Colatino/zeropedal/pictures/assembly/WhatsApp Image 2022-07-04 at 21.12.30 (3).jpeg

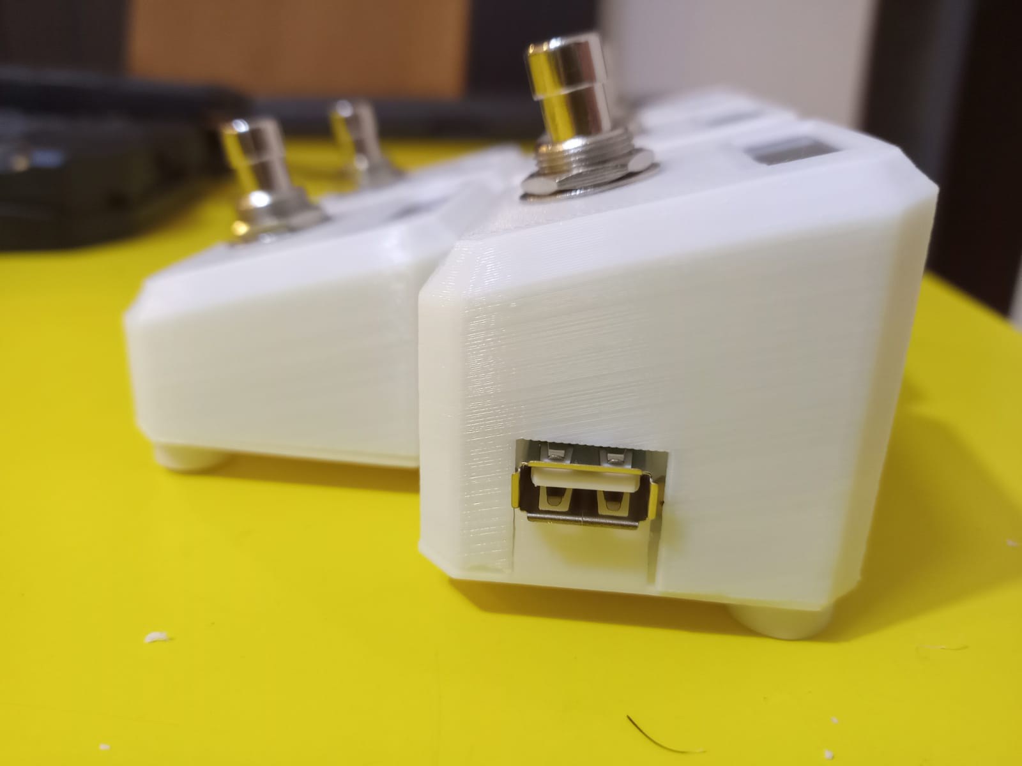
pictures/assembly/WhatsApp Image 2022-07-04 at 21.12.30 (3).jpeg
