Colatino/zeropedal/g1xfour.py

# Effects list for the Zoom G1XFour
# Each effect on this list follows the format:
# ['name',id,group,'filename',nslots,nparam,[params]]
# 'name' - display name of the effect on the pedal
# id - unique identification number for that effect as given by zoom
# group - the group number
# 'filename' - name of the pedal icon file
# nslots - number of slots that the effect occupies on the chain
# nparam - number of parameters for the effect
# param - list of the parameters for this effect with the format:
# [pedal,min,max,cur,'name']
# pedal - bool that tells if the effect makes use of the expression pedal 
# min - minimum value for the parameter
# max - maximum value for the parameter
# cur - current value for the parameter
# 'name' - display name of the parameter
effects = [
['Bypass',0,0,'',1,0,[[0, 0, 0, 0, '-'],[0, 0, 0, 0, '-'],[0, 0, 0, 0, '-'],[0, 0, 0, 0, '-'],[0, 0, 0, 0, '-'],[0, 0, 0, 0, '-'],[0, 0, 0, 0, '-'],[0, 0, 0, 0, '-']]],
['Comp',16777232,1,'COMP.ZD2.BMP',1,4,[[0, 10, 6, 0, 'Sense'],[0, 1, 0, 0, 'ATTCK'],[0, 10, 6, 0, 'Tone'],[0, 100, 80, 0, 'VOL'],[0, 0, 0, 0, '-'],[0, 0, 0, 0, '-'],[0, 0, 0, 0, '-'],[0, 0, 0, 0, '-']]],
['RackComp',16777248,1,'RACKCOMP.ZD2.BMP',1,4,[[0, 50, 40, 0, 'THRSH'],[0, 9, 5, 0, 'Ratio'],[0, 9, 6, 0, 'ATTCK'],[0, 100, 80, 0, 'VOL'],[0, 0, 0, 0, '-'],[0, 0, 0, 0, '-'],[0, 0, 0, 0, '-'],[0, 0, 0, 0, '-']]],
['SlowATTCK',16777264,1,'SLWATK.ZD2.BMP',1,4,[[0, 49, 20, 0, 'Time'],[0, 10, 10, 0, 'Curve'],[0, 100, 100, 0, 'Tone'],[0, 100, 80, 0, 'VOL'],[0, 0, 0, 0, '-'],[0, 0, 0, 0, '-'],[0, 0, 0, 0, '-'],[0, 0, 0, 0, '-']]],
['ZNR',16777280,1,'ZNR.ZD2.BMP',1,4,[[0, 1, 1, 0, 'DETCT'],[0, 100, 100, 0, 'Depth'],[0, 100, 30, 0, 'THRSH'],[0, 100, 0, 0, 'Decay'],[0, 0, 0, 0, '-'],[0, 0, 0, 0, '-'],[0, 0, 0, 0, '-'],[0, 0, 0, 0, '-']]],
['MuteSW',16777296,1,'MUTESW.ZD2.BMP',1,4,[[0, 100, 13, 0, 'Edge'],[0, 100, 100, 0, 'Speed'],[0, 1, 0, 0, 'INVRT'],[0, 2, 1, 0, 'ON/OFF'],[0, 0, 0, 0, '-'],[0, 0, 0, 0, '-'],[0, 0, 0, 0, '-'],[0, 0, 0, 0, '-']]],
['GrayComp',16777312,1,'GRAYCOMP.ZD2.BMP',1,4,[[0, 100, 63, 0, 'SUSTN'],[0, 100, 50, 0, 'Lo'],[0, 100, 50, 0, 'Hi'],[0, 100, 88, 0, 'VOL'],[0, 0, 0, 0, '-'],[0, 0, 0, 0, '-'],[0, 0, 0, 0, '-'],[0, 0, 0, 0, '-']]],
['NoiseGate',16777328,1,'N_GATE.ZD2.BMP',1,4,[[0, 1, 1, 0, 'DETCT'],[0, 100, 100, 0, 'Depth'],[0, 100, 54, 0, 'THRSH'],[0, 100, 0, 0, 'Decay'],[0, 0, 0, 0, '-'],[0, 0, 0, 0, '-'],[0, 0, 0, 0, '-'],[0, 0, 0, 0, '-']]],
['OptComp',16777344,1,'OPTCOMP.ZD2.BMP',1,4,[[0, 10, 7, 0, 'Drive'],[0, 100, 50, 0, 'Lo'],[0, 100, 50, 0, 'Hi'],[0, 100, 60, 0, 'VOL'],[0, 0, 0, 0, '-'],[0, 0, 0, 0, '-'],[0, 0, 0, 0, '-'],[0, 0, 0, 0, '-']]],
['BlackOpt',25165840,1,'BLACKOPT.ZD2.BMP',1,4,[[0, 100, 50, 0, 'Comp'],[0, 100, 50, 0, 'Lo'],[0, 100, 50, 0, 'Hi'],[0, 100, 76, 0, 'VOL'],[0, 0, 0, 0, '-'],[0, 0, 0, 0, '-'],[0, 0, 0, 0, '-'],[0, 0, 0, 0, '-']]],
['LMT-76',25165856,1,'LMT1176.ZD2.BMP',1,4,[[0, 80, 40, 0, 'Input'],[0, 3, 0, 0, 'Ratio'],[0, 60, 10, 0, 'REL'],[0, 80, 38, 0, 'Output'],[0, 0, 0, 0, '-'],[0, 0, 0, 0, '-'],[0, 0, 0, 0, '-'],[0, 0, 0, 0, '-']]],
['AutoWah',33554448,2,'AUTOWAH.ZD2.BMP',1,4,[[0, 1, 1, 0, 'Mode'],[0, 9, 7, 0, 'Sense'],[0, 10, 8, 0, 'RESO'],[0, 100, 80, 0, 'VOL'],[0, 0, 0, 0, '-'],[0, 0, 0, 0, '-'],[0, 0, 0, 0, '-'],[0, 0, 0, 0, '-']]],
['Resonance',33554464,2,'RESONANC.ZD2.BMP',1,4,[[0, 1, 1, 0, 'Mode'],[0, 9, 4, 0, 'Sense'],[0, 10, 8, 0, 'RESO'],[0, 100, 80, 0, 'VOL'],[0, 0, 0, 0, '-'],[0, 0, 0, 0, '-'],[0, 0, 0, 0, '-'],[0, 0, 0, 0, '-']]],
['Cry',33554480,2,'CRY.ZD2.BMP',1,4,[[0, 9, 6, 0, 'Range'],[0, 10, 8, 0, 'RESO'],[0, 19, 16, 0, 'Sense'],[0, 100, 100, 0, 'BAL'],[0, 0, 0, 0, '-'],[0, 0, 0, 0, '-'],[0, 0, 0, 0, '-'],[0, 0, 0, 0, '-']]],
['SeqFLTR',33554496,2,'SEQFLTR.ZD2.BMP',1,4,[[0, 6, 6, 0, 'Step'],[0, 7, 6, 0, 'PTTRN'],[0, 77, 25, 0, 'Speed'],[0, 10, 10, 0, 'RESO'],[0, 0, 0, 0, '-'],[0, 0, 0, 0, '-'],[0, 0, 0, 0, '-'],[0, 0, 0, 0, '-']]],
['Gt GEQ',33554513,2,'GT_GEQ1U.ZD2.BMP',2,7,[[0, 48, 24, 0, '160'],[0, 48, 24, 0, '400'],[0, 48, 24, 0, '800'],[0, 48, 24, 0, '3.2k'],[0, 48, 24, 0, '6.4k'],[0, 48, 24, 0, '12k'],[0, 100, 80, 0, 'VOL'],[0, 0, 0, 0, '-']]],
['Gt GEQ 7',33554516,2,'GTGEQ71U.ZD2.BMP',2,8,[[0, 48, 24, 0, '100'],[0, 48, 24, 0, '200'],[0, 48, 24, 0, '400'],[0, 48, 24, 0, '800'],[0, 48, 24, 0, '1.6k'],[0, 48, 24, 0, '3.2k'],[0, 48, 24, 0, '6.4k'],[0, 100, 80, 0, 'VOL']]],
['St Gt GEQ',33554529,2,'STGTGE1U.ZD2.BMP',2,7,[[0, 48, 24, 0, '160'],[0, 48, 24, 0, '400'],[0, 48, 24, 0, '800'],[0, 48, 24, 0, '3.2k'],[0, 48, 24, 0, '6.4k'],[0, 48, 24, 0, '12k'],[0, 100, 80, 0, 'VOL'],[0, 0, 0, 0, '-']]],
['ParaEQ',33554544,2,'PARAEQ.ZD2.BMP',1,4,[[0, 30, 8, 0, 'FREQ'],[0, 67, 1, 0, 'Q'],[0, 48, 24, 0, 'Gain'],[0, 100, 80, 0, 'VOL'],[0, 0, 0, 0, '-'],[0, 0, 0, 0, '-'],[0, 0, 0, 0, '-'],[0, 0, 0, 0, '-']]],
['RndmFLTR',33554576,2,'RNDMFLTR.ZD2.BMP',1,4,[[0, 2, 2, 0, 'Type'],[0, 77, 34, 0, 'Speed'],[0, 100, 90, 0, 'BAL'],[0, 100, 80, 0, 'VOL'],[0, 0, 0, 0, '-'],[0, 0, 0, 0, '-'],[0, 0, 0, 0, '-'],[0, 0, 0, 0, '-']]],
['LowPassFL',33554592,2,'LOWPASSF.ZD2.BMP',1,4,[[0, 100, 56, 0, 'FREQ'],[0, 201, 50, 0, 'Sense'],[0, 21, 3, 0, 'RESO'],[0, 100, 100, 0, 'BAL'],[0, 0, 0, 0, '-'],[0, 0, 0, 0, '-'],[0, 0, 0, 0, '-'],[0, 0, 0, 0, '-']]],
['Exciter',33554608,2,'EXCITER.ZD2.BMP',1,4,[[0, 100, 0, 0, 'Bass'],[0, 100, 0, 0, 'Treble'],[0, 100, 80, 0, 'VOL'],[0, 1, 0, 0, 'ON/OFF'],[0, 0, 0, 0, '-'],[0, 0, 0, 0, '-'],[0, 0, 0, 0, '-'],[0, 0, 0, 0, '-']]],
['Step',33554624,2,'STEP.ZD2.BMP',1,4,[[0, 100, 60, 0, 'Depth'],[0, 78, 25, 0, 'Rate'],[0, 10, 8, 0, 'RESO'],[0, 10, 10, 0, 'Shape'],[0, 0, 0, 0, '-'],[0, 0, 0, 0, '-'],[0, 0, 0, 0, '-'],[0, 0, 0, 0, '-']]],
['LFO FLTR',33554640,2,'LFO_FLTR.ZD2.BMP',1,4,[[0, 100, 100, 0, 'Depth'],[0, 77, 57, 0, 'Rate'],[0, 10, 8, 0, 'RESO'],[0, 3, 0, 0, 'Wave'],[0, 0, 0, 0, '-'],[0, 0, 0, 0, '-'],[0, 0, 0, 0, '-'],[0, 0, 0, 0, '-']]],
['TS Drive',50331664,3,'TS_DRIVE.ZD2.BMP',1,4,[[0, 100, 74, 0, 'Gain'],[0, 1, 0, 0, 'Boost'],[0, 100, 57, 0, 'Tone'],[0, 100, 82, 0, 'VOL'],[0, 0, 0, 0, '-'],[0, 0, 0, 0, '-'],[0, 0, 0, 0, '-'],[0, 0, 0, 0, '-']]],
['EP Stomp',50331680,3,'EP_STOMP.ZD2.BMP',1,4,[[0, 100, 35, 0, 'Gain'],[0, 20, 10, 0, 'Bass'],[0, 20, 8, 0, 'Treble'],[0, 100, 62, 0, 'VOL'],[0, 0, 0, 0, '-'],[0, 0, 0, 0, '-'],[0, 0, 0, 0, '-'],[0, 0, 0, 0, '-']]],
['RC Boost',50331696,3,'RCBOOST.ZD2.BMP',1,4,[[0, 100, 58, 0, 'Gain'],[0, 100, 48, 0, 'Bass'],[0, 100, 52, 0, 'Treble'],[0, 100, 48, 0, 'VOL'],[0, 0, 0, 0, '-'],[0, 0, 0, 0, '-'],[0, 0, 0, 0, '-'],[0, 0, 0, 0, '-']]],
['GoldDrive',50331712,3,'GOLD_DRV.ZD2.BMP',1,4,[[0, 100, 69, 0, 'Gain'],[0, 100, 50, 0, 'Bass'],[0, 100, 56, 0, 'Treble'],[0, 100, 43, 0, 'VOL'],[0, 0, 0, 0, '-'],[0, 0, 0, 0, '-'],[0, 0, 0, 0, '-'],[0, 0, 0, 0, '-']]],
['SweetDrv',50331728,3,'SWEETDRV.ZD2.BMP',1,4,[[0, 100, 78, 0, 'Gain'],[0, 100, 50, 0, 'Tone'],[0, 100, 67, 0, 'Focus'],[0, 100, 62, 0, 'VOL'],[0, 0, 0, 0, '-'],[0, 0, 0, 0, '-'],[0, 0, 0, 0, '-'],[0, 0, 0, 0, '-']]],
['DYN Drive',50331744,3,'DYNDRIVE.ZD2.BMP',1,4,[[0, 100, 78, 0, 'Gain'],[0, 100, 67, 0, 'Tone'],[0, 1, 1, 0, 'Mode'],[0, 100, 46, 0, 'VOL'],[0, 0, 0, 0, '-'],[0, 0, 0, 0, '-'],[0, 0, 0, 0, '-'],[0, 0, 0, 0, '-']]],
['RedCrunch',50331760,3,'REDCRUNC.ZD2.BMP',1,4,[[0, 100, 68, 0, 'Gain'],[0, 100, 47, 0, 'Tone'],[0, 100, 48, 0, 'PRSNC'],[0, 100, 61, 0, 'VOL'],[0, 0, 0, 0, '-'],[0, 0, 0, 0, '-'],[0, 0, 0, 0, '-'],[0, 0, 0, 0, '-']]],
['MetalWRLD',50331776,3,'MTLWRLD.ZD2.BMP',1,4,[[0, 100, 60, 0, 'Gain'],[0, 100, 50, 0, 'Bass'],[0, 100, 50, 0, 'Treble'],[0, 100, 80, 0, 'VOL'],[0, 0, 0, 0, '-'],[0, 0, 0, 0, '-'],[0, 0, 0, 0, '-'],[0, 0, 0, 0, '-']]],
['TB MK1.5',50331792,3,'TB_MK15.ZD2.BMP',1,4,[[0, 100, 90, 0, 'ATTCK'],[0, 100, 100, 0, 'Tone'],[0, 1, 1, 0, 'Color'],[0, 100, 92, 0, 'VOL'],[0, 0, 0, 0, '-'],[0, 0, 0, 0, '-'],[0, 0, 0, 0, '-'],[0, 0, 0, 0, '-']]],
['OctFuzz',50331808,3,'OCTFUZZ.ZD2.BMP',1,4,[[0, 100, 65, 0, 'Boost'],[0, 1, 1, 0, 'Color'],[0, 100, 50, 0, 'Tone'],[0, 100, 68, 0, 'VOL'],[0, 0, 0, 0, '-'],[0, 0, 0, 0, '-'],[0, 0, 0, 0, '-'],[0, 0, 0, 0, '-']]],
['SpotBoost',50331824,3,'SPTBOOST.ZD2.BMP',1,4,[[0, 100, 35, 0, 'Boost'],[0, 20, 10, 0, 'Bass'],[0, 20, 8, 0, 'Treble'],[0, 1, 1, 0, 'ON/OFF'],[0, 0, 0, 0, '-'],[0, 0, 0, 0, '-'],[0, 0, 0, 0, '-'],[0, 0, 0, 0, '-']]],
['Aco.Sim',50331840,3,'ACOSIM.ZD2.BMP',1,4,[[0, 100, 80, 0, 'Top'],[0, 100, 50, 0, 'Body'],[0, 100, 100, 0, 'Tone'],[0, 100, 80, 0, 'VOL'],[0, 0, 0, 0, '-'],[0, 0, 0, 0, '-'],[0, 0, 0, 0, '-'],[0, 0, 0, 0, '-']]],
['NYC Muff',50331856,3,'NYC_MUFF.ZD2.BMP',1,4,[[0, 100, 70, 0, 'SUSTN'],[0, 100, 55, 0, 'Tone'],[0, 100, 100, 0, 'BAL'],[0, 100, 58, 0, 'VOL'],[0, 0, 0, 0, '-'],[0, 0, 0, 0, '-'],[0, 0, 0, 0, '-'],[0, 0, 0, 0, '-']]],
['HG THRTTL',50331872,3,'BGTHRTTL.ZD2.BMP',1,4,[[0, 100, 78, 0, 'Gain'],[0, 100, 56, 0, 'Tone'],[0, 100, 46, 0, 'MdCut'],[0, 100, 54, 0, 'VOL'],[0, 0, 0, 0, '-'],[0, 0, 0, 0, '-'],[0, 0, 0, 0, '-'],[0, 0, 0, 0, '-']]],
['BG GRID',50331888,3,'BG_GRID.ZD2.BMP',1,4,[[0, 100, 68, 0, 'Gain'],[0, 100, 50, 0, 'Tone'],[0, 100, 100, 0, 'BAL'],[0, 100, 74, 0, 'VOL'],[0, 0, 0, 0, '-'],[0, 0, 0, 0, '-'],[0, 0, 0, 0, '-'],[0, 0, 0, 0, '-']]],
['DIST 1',50331936,3,'DIST_1.ZD2.BMP',1,4,[[0, 100, 61, 0, 'Gain'],[0, 100, 41, 0, 'Tone'],[0, 100, 100, 0, 'VOL'],[0, 1, 0, 0, 'Comp'],[0, 0, 0, 0, '-'],[0, 0, 0, 0, '-'],[0, 0, 0, 0, '-'],[0, 0, 0, 0, '-']]],
['Squeak',50331952,3,'SQUEAK.ZD2.BMP',1,4,[[0, 100, 47, 0, 'Gain'],[0, 100, 60, 0, 'FLTR'],[0, 100, 79, 0, 'VOL'],[0, 100, 0, 0, 'DryMx'],[0, 0, 0, 0, '-'],[0, 0, 0, 0, '-'],[0, 0, 0, 0, '-'],[0, 0, 0, 0, '-']]],
['UpOctBSTR',50331968,3,'UPOCTBST.ZD2.BMP',1,4,[[0, 100, 65, 0, 'UpOct'],[0, 100, 47, 0, 'DryMx'],[0, 100, 75, 0, 'Bottom'],[0, 100, 70, 0, 'PRSNC'],[0, 0, 0, 0, '-'],[0, 0, 0, 0, '-'],[0, 0, 0, 0, '-'],[0, 0, 0, 0, '-']]],
['OutputBST',50331984,3,'OUT_BST.ZD2.BMP',1,4,[[0, 9, 4, 0, 'Range'],[0, 100, 30, 0, 'Boost'],[0, 100, 50, 0, 'Tone'],[0, 100, 80, 0, 'VOL'],[0, 0, 0, 0, '-'],[0, 0, 0, 0, '-'],[0, 0, 0, 0, '-'],[0, 0, 0, 0, '-']]],
['DIST Plus',50332000,3,'DISTPLUS.ZD2.BMP',1,4,[[0, 100, 70, 0, 'Gain'],[0, 100, 100, 0, 'VOL'],[0, 100, 0, 0, 'DryMx'],[0, 2, 0, 0, 'Comp'],[0, 0, 0, 0, '-'],[0, 0, 0, 0, '-'],[0, 0, 0, 0, '-'],[0, 0, 0, 0, '-']]],
['Zen O.DRV',50332016,3,'ZEN_DRV.ZD2.BMP',1,4,[[0, 100, 70, 0, 'Gain'],[0, 100, 60, 0, 'Tone'],[0, 100, 80, 0, 'Voice'],[0, 100, 70, 0, 'VOL'],[0, 0, 0, 0, '-'],[0, 0, 0, 0, '-'],[0, 0, 0, 0, '-'],[0, 0, 0, 0, '-']]],
['VioletDST',50332048,3,'VIOLETDS.ZD2.BMP',1,4,[[0, 100, 70, 0, 'Gain'],[0, 100, 80, 0, 'Tone'],[0, 2, 2, 0, 'Voice'],[0, 100, 70, 0, 'VOL'],[0, 0, 0, 0, '-'],[0, 0, 0, 0, '-'],[0, 0, 0, 0, '-'],[0, 0, 0, 0, '-']]],
['MS 800',67108881,4,'MS800_1U.ZD2.BMP',2,7,[[0, 1, 1, 0, 'Input'],[0, 100, 50, 0, 'Bass'],[0, 100, 50, 0, 'MID'],[0, 100, 50, 0, 'Treble'],[0, 100, 30, 0, 'PRSNC'],[0, 100, 70, 0, 'Gain'],[0, 100, 70, 0, 'VOL'],[0, 0, 0, 0, '-']]],
['MS 1959',67108889,4,'MS19591U.ZD2.BMP',2,7,[[0, 100, 50, 0, 'Bass'],[0, 100, 70, 0, 'MID'],[0, 100, 60, 0, 'Treble'],[0, 100, 40, 0, 'PRSNC'],[0, 101, 61, 0, 'Input1'],[0, 101, 0, 0, 'Input2'],[0, 100, 80, 0, 'VOL'],[0, 0, 0, 0, '-']]],
['MS 45os',67108891,4,'MS45OS1U.ZD2.BMP',2,7,[[0, 100, 30, 0, 'Bass'],[0, 100, 70, 0, 'MID'],[0, 100, 65, 0, 'Treble'],[0, 100, 30, 0, 'PRSNC'],[0, 101, 61, 0, 'Input1'],[0, 101, 0, 0, 'Input2'],[0, 100, 80, 0, 'VOL'],[0, 0, 0, 0, '-']]],
['FD TWNR',67108897,4,'FD_TWR1U.ZD2.BMP',2,8,[[0, 90, 38, 0, 'Bass'],[0, 90, 40, 0, 'MID'],[0, 90, 35, 0, 'Treble'],[0, 1, 0, 0, 'BRGHT'],[0, 90, 30, 0, 'Gain'],[0, 90, 70, 0, 'VOL'],[0, 90, 0, 0, 'Depth'],[0, 100, 40, 0, 'Speed']]],
['FD B-MAN',67108904,4,'FDBMAN1U.ZD2.BMP',2,7,[[0, 1, 1, 0, 'Input'],[0, 110, 30, 0, 'Bass'],[0, 110, 90, 0, 'MID'],[0, 110, 40, 0, 'Treble'],[0, 110, 50, 0, 'PRSNC'],[0, 110, 30, 0, 'Gain'],[0, 110, 50, 0, 'VOL'],[0, 0, 0, 0, '-']]],
['FD DLXR',67108908,4,'FDDLXR1U.ZD2.BMP',2,7,[[0, 1, 0, 0, 'Input'],[0, 90, 33, 0, 'Bass'],[0, 90, 55, 0, 'Treble'],[0, 90, 50, 0, 'Gain'],[0, 90, 90, 0, 'VOL'],[0, 90, 0, 0, 'Depth'],[0, 100, 40, 0, 'Speed'],[0, 0, 0, 0, '-']]],
['FD MASTER',67108909,4,'FDMSTR1U.ZD2.BMP',2,6,[[0, 90, 40, 0, 'Gain'],[0, 90, 60, 0, 'Bass'],[0, 90, 60, 0, 'MID'],[0, 90, 60, 0, 'Treble'],[0, 1, 1, 0, 'Fat'],[0, 90, 40, 0, 'VOL'],[0, 0, 0, 0, '-'],[0, 0, 0, 0, '-']]],
['UK 30A',67108913,4,'UK30A_1U.ZD2.BMP',2,7,[[0, 100, 49, 0, 'Bass'],[0, 100, 38, 0, 'Treble'],[0, 100, 78, 0, 'Cut'],[0, 100, 30, 0, 'Gain'],[0, 100, 84, 0, 'VOL'],[0, 100, 0, 0, 'Depth'],[0, 110, 50, 0, 'Speed'],[0, 0, 0, 0, '-']]],
['BG MK1',67108929,4,'BGMK1_1U.ZD2.BMP',2,7,[[0, 100, 49, 0, 'Bass'],[0, 100, 55, 0, 'MID'],[0, 100, 53, 0, 'Treble'],[0, 100, 55, 0, 'PRSNC'],[0, 100, 72, 0, 'Gain1'],[0, 100, 70, 0, 'Gain2'],[0, 100, 58, 0, 'VOL'],[0, 0, 0, 0, '-']]],
['BG MK3',67108931,4,'BGMK3_1U.ZD2.BMP',2,7,[[0, 100, 52, 0, 'Bass'],[0, 100, 85, 0, 'MID'],[0, 100, 40, 0, 'Treble'],[0, 100, 40, 0, 'PRSNC'],[0, 100, 75, 0, 'Gain1'],[0, 100, 75, 0, 'Gain2'],[0, 100, 78, 0, 'VOL'],[0, 0, 0, 0, '-']]],
['XtasyBlue',67108945,4,'XTSBLU1U.ZD2.BMP',2,7,[[0, 100, 50, 0, 'Bass'],[0, 100, 50, 0, 'MID'],[0, 100, 50, 0, 'Treble'],[0, 100, 40, 0, 'PRSNC'],[0, 1, 1, 0, 'STRCT'],[0, 100, 60, 0, 'Gain'],[0, 100, 42, 0, 'VOL'],[0, 0, 0, 0, '-']]],
['HW 100',67108961,4,'HW100_1U.ZD2.BMP',2,7,[[0, 1, 1, 0, 'Input'],[0, 100, 40, 0, 'Bass'],[0, 100, 80, 0, 'MID'],[0, 100, 60, 0, 'Treble'],[0, 100, 60, 0, 'PRSNC'],[0, 100, 50, 0, 'Gain'],[0, 100, 60, 0, 'VOL'],[0, 0, 0, 0, '-']]],
['Recti ORG',67108977,4,'RCTORG1U.ZD2.BMP',2,7,[[0, 1, 0, 0, 'Mode'],[0, 100, 52, 0, 'Bass'],[0, 100, 65, 0, 'MID'],[0, 100, 67, 0, 'Treble'],[0, 100, 62, 0, 'PRSNC'],[0, 100, 70, 0, 'Gain'],[0, 100, 62, 0, 'VOL'],[0, 0, 0, 0, '-']]],
['ORG120',67108993,4,'ORG1201U.ZD2.BMP',2,7,[[0, 1, 1, 0, 'Input'],[0, 5, 3, 0, 'Color'],[0, 100, 50, 0, 'Bass'],[0, 100, 60, 0, 'Treble'],[0, 100, 50, 0, 'PRSNC'],[0, 100, 53, 0, 'Gain'],[0, 100, 100, 0, 'VOL'],[0, 0, 0, 0, '-']]],
['DZ DRV',67109009,4,'DZ_DRV1U.ZD2.BMP',2,8,[[0, 100, 50, 0, 'Bass'],[0, 100, 70, 0, 'MID'],[0, 100, 60, 0, 'Treble'],[0, 100, 40, 0, 'PRSNC'],[0, 100, 60, 0, 'Gain'],[0, 100, 80, 0, 'VOL'],[0, 100, 0, 0, 'Deep'],[0, 100, 0, 0, 'MidCut']]],
['MATCH30',67109025,4,'MACH301U.ZD2.BMP',2,7,[[0, 101, 36, 0, 'Gain1'],[0, 100, 47, 0, 'Bass1'],[0, 100, 49, 0, 'TRBL1'],[0, 101, 0, 0, 'Gain2'],[0, 5, 1, 0, 'Tone2'],[0, 100, 0, 0, 'Cut'],[0, 101, 34, 0, 'VOL'],[0, 0, 0, 0, '-']]],
['MS4x12',83886096,5,'MS4X12.ZD2.BMP',1,4,[[0, 1, 0, 0, 'MIC'],[0, 100, 50, 0, 'D57:D421'],[0, 100, 50, 0, 'Hi'],[0, 100, 50, 0, 'Lo'],[0, 0, 0, 0, '-'],[0, 0, 0, 0, '-'],[0, 0, 0, 0, '-'],[0, 0, 0, 0, '-']]],
['MS4x12GB',83886104,5,'MS4X12GB.ZD2.BMP',1,4,[[0, 1, 0, 0, 'MIC'],[0, 100, 50, 0, 'D57:D421'],[0, 100, 50, 0, 'Hi'],[0, 100, 50, 0, 'Lo'],[0, 0, 0, 0, '-'],[0, 0, 0, 0, '-'],[0, 0, 0, 0, '-'],[0, 0, 0, 0, '-']]],
['MS4x12AL',83886106,5,'MS4X12AL.ZD2.BMP',1,4,[[0, 1, 0, 0, 'MIC'],[0, 100, 50, 0, 'D57:D421'],[0, 100, 50, 0, 'Hi'],[0, 100, 50, 0, 'Lo'],[0, 0, 0, 0, '-'],[0, 0, 0, 0, '-'],[0, 0, 0, 0, '-'],[0, 0, 0, 0, '-']]],
['FD2x12',83886112,5,'FD2X12.ZD2.BMP',1,4,[[0, 1, 0, 0, 'MIC'],[0, 100, 50, 0, 'D57:D421'],[0, 100, 50, 0, 'Hi'],[0, 100, 50, 0, 'Lo'],[0, 0, 0, 0, '-'],[0, 0, 0, 0, '-'],[0, 0, 0, 0, '-'],[0, 0, 0, 0, '-']]],
['FD-B4x10',83886119,5,'FDB4X10.ZD2.BMP',1,4,[[0, 1, 0, 0, 'MIC'],[0, 100, 50, 0, 'D57:D421'],[0, 100, 50, 0, 'Hi'],[0, 100, 50, 0, 'Lo'],[0, 0, 0, 0, '-'],[0, 0, 0, 0, '-'],[0, 0, 0, 0, '-'],[0, 0, 0, 0, '-']]],
['FD-DX1x12',83886122,5,'FDDX1X12.ZD2.BMP',1,4,[[0, 1, 0, 0, 'MIC'],[0, 100, 50, 0, 'D57:D421'],[0, 100, 50, 0, 'Hi'],[0, 100, 50, 0, 'Lo'],[0, 0, 0, 0, '-'],[0, 0, 0, 0, '-'],[0, 0, 0, 0, '-'],[0, 0, 0, 0, '-']]],
['FD MA2x12',83886123,5,'FDMA2X12.ZD2.BMP',1,4,[[0, 1, 0, 0, 'MIC'],[0, 100, 50, 0, 'D57:D421'],[0, 100, 50, 0, 'Hi'],[0, 100, 50, 0, 'Lo'],[0, 0, 0, 0, '-'],[0, 0, 0, 0, '-'],[0, 0, 0, 0, '-'],[0, 0, 0, 0, '-']]],
['UK2x12',83886128,5,'UK2X12.ZD2.BMP',1,4,[[0, 1, 0, 0, 'MIC'],[0, 100, 50, 0, 'D57:D421'],[0, 100, 50, 0, 'Hi'],[0, 100, 50, 0, 'Lo'],[0, 0, 0, 0, '-'],[0, 0, 0, 0, '-'],[0, 0, 0, 0, '-'],[0, 0, 0, 0, '-']]],
['MK1 1x12',83886144,5,'MK1_1X12.ZD2.BMP',1,4,[[0, 1, 0, 0, 'MIC'],[0, 100, 50, 0, 'D57:D421'],[0, 100, 50, 0, 'Hi'],[0, 100, 50, 0, 'Lo'],[0, 0, 0, 0, '-'],[0, 0, 0, 0, '-'],[0, 0, 0, 0, '-'],[0, 0, 0, 0, '-']]],
['MK3 1x12',83886146,5,'MK3_1X12.ZD2.BMP',1,4,[[0, 1, 0, 0, 'MIC'],[0, 100, 50, 0, 'D57:D421'],[0, 100, 50, 0, 'Hi'],[0, 100, 50, 0, 'Lo'],[0, 0, 0, 0, '-'],[0, 0, 0, 0, '-'],[0, 0, 0, 0, '-'],[0, 0, 0, 0, '-']]],
['BGN4x12',83886160,5,'BGN4X12.ZD2.BMP',1,4,[[0, 1, 0, 0, 'MIC'],[0, 100, 50, 0, 'D57:D421'],[0, 100, 50, 0, 'Hi'],[0, 100, 50, 0, 'Lo'],[0, 0, 0, 0, '-'],[0, 0, 0, 0, '-'],[0, 0, 0, 0, '-'],[0, 0, 0, 0, '-']]],
['HW4x12',83886176,5,'HW4X12.ZD2.BMP',1,4,[[0, 1, 0, 0, 'MIC'],[0, 100, 50, 0, 'D57:D421'],[0, 100, 50, 0, 'Hi'],[0, 100, 50, 0, 'Lo'],[0, 0, 0, 0, '-'],[0, 0, 0, 0, '-'],[0, 0, 0, 0, '-'],[0, 0, 0, 0, '-']]],
['RCT4x12',83886192,5,'RCT4X12.ZD2.BMP',1,4,[[0, 1, 0, 0, 'MIC'],[0, 100, 50, 0, 'D57:D421'],[0, 100, 50, 0, 'Hi'],[0, 100, 50, 0, 'Lo'],[0, 0, 0, 0, '-'],[0, 0, 0, 0, '-'],[0, 0, 0, 0, '-'],[0, 0, 0, 0, '-']]],
['ORG4x12',83886208,5,'ORG_4X12.ZD2.BMP',1,4,[[0, 1, 0, 0, 'MIC'],[0, 100, 50, 0, 'D57:D421'],[0, 100, 50, 0, 'Hi'],[0, 100, 50, 0, 'Lo'],[0, 0, 0, 0, '-'],[0, 0, 0, 0, '-'],[0, 0, 0, 0, '-'],[0, 0, 0, 0, '-']]],
['DZ4x12F',83886224,5,'DZ4X12F.ZD2.BMP',1,4,[[0, 1, 0, 0, 'MIC'],[0, 100, 50, 0, 'D57:D421'],[0, 100, 50, 0, 'Hi'],[0, 100, 50, 0, 'Lo'],[0, 0, 0, 0, '-'],[0, 0, 0, 0, '-'],[0, 0, 0, 0, '-'],[0, 0, 0, 0, '-']]],
['MA2x12',83886240,5,'MA2X12.ZD2.BMP',1,4,[[0, 1, 0, 0, 'MIC'],[0, 100, 50, 0, 'D57:D421'],[0, 100, 50, 0, 'Hi'],[0, 100, 50, 0, 'Lo'],[0, 0, 0, 0, '-'],[0, 0, 0, 0, '-'],[0, 0, 0, 0, '-'],[0, 0, 0, 0, '-']]],
['Tremolo',100663312,6,'TREMOLO.ZD2.BMP',1,4,[[0, 2, 0, 0, 'Wave'],[0, 100, 90, 0, 'Depth'],[0, 110, 50, 0, 'Rate'],[0, 100, 62, 0, 'VOL'],[0, 0, 0, 0, '-'],[0, 0, 0, 0, '-'],[0, 0, 0, 0, '-'],[0, 0, 0, 0, '-']]],
['Chorus',100663328,6,'CHORUS.ZD2.BMP',1,4,[[0, 100, 40, 0, 'Depth'],[0, 49, 24, 0, 'Rate'],[0, 10, 7, 0, 'Tone'],[0, 100, 50, 0, 'Mix'],[0, 0, 0, 0, '-'],[0, 0, 0, 0, '-'],[0, 0, 0, 0, '-'],[0, 0, 0, 0, '-']]],
['StereoCho',100663344,6,'STEREOCH.ZD2.BMP',1,4,[[0, 100, 80, 0, 'Depth'],[0, 49, 29, 0, 'Rate'],[0, 10, 7, 0, 'Tone'],[0, 100, 60, 0, 'Mix'],[0, 0, 0, 0, '-'],[0, 0, 0, 0, '-'],[0, 0, 0, 0, '-'],[0, 0, 0, 0, '-']]],
['Phaser',100663360,6,'PHASER.ZD2.BMP',1,4,[[0, 3, 3, 0, 'Color'],[0, 100, 100, 0, 'Depth'],[0, 77, 11, 0, 'Rate'],[0, 100, 50, 0, 'RESO'],[0, 0, 0, 0, '-'],[0, 0, 0, 0, '-'],[0, 0, 0, 0, '-'],[0, 0, 0, 0, '-']]],
['VinFLNGR',100663376,6,'VINFLNGR.ZD2.BMP',1,4,[[0, 50, 4, 0, 'PreD'],[0, 100, 47, 0, 'Depth'],[0, 78, 7, 0, 'Rate'],[0, 20, 18, 0, 'RESO'],[0, 0, 0, 0, '-'],[0, 0, 0, 0, '-'],[0, 0, 0, 0, '-'],[0, 0, 0, 0, '-']]],
['TheVibe',100663392,6,'THEVIBE.ZD2.BMP',1,4,[[0, 50, 25, 0, 'Speed'],[0, 100, 60, 0, 'Depth'],[0, 1, 1, 0, 'Mode'],[0, 100, 80, 0, 'VOL'],[0, 0, 0, 0, '-'],[0, 0, 0, 0, '-'],[0, 0, 0, 0, '-'],[0, 0, 0, 0, '-']]],
['Vibrato',100663408,6,'VIBRATO.ZD2.BMP',1,4,[[0, 100, 40, 0, 'Depth'],[0, 78, 30, 0, 'Rate'],[0, 10, 7, 0, 'Tone'],[0, 100, 72, 0, 'BAL'],[0, 0, 0, 0, '-'],[0, 0, 0, 0, '-'],[0, 0, 0, 0, '-'],[0, 0, 0, 0, '-']]],
['Octave',100663424,6,'OCTAVE.ZD2.BMP',1,4,[[0, 100, 80, 0, 'OCT1'],[0, 100, 15, 0, 'OCT2'],[0, 10, 8, 0, 'Tone'],[0, 100, 100, 0, 'Dry'],[0, 0, 0, 0, '-'],[0, 0, 0, 0, '-'],[0, 0, 0, 0, '-'],[0, 0, 0, 0, '-']]],
['RingMod',100663440,6,'RINGMOD.ZD2.BMP',1,4,[[0, 49, 27, 0, 'FREQ'],[0, 10, 10, 0, 'Tone'],[0, 100, 50, 0, 'BAL'],[0, 100, 88, 0, 'VOL'],[0, 0, 0, 0, '-'],[0, 0, 0, 0, '-'],[0, 0, 0, 0, '-'],[0, 0, 0, 0, '-']]],
['Detune',100663456,6,'DETUNE.ZD2.BMP',1,4,[[0, 50, 35, 0, 'Cent'],[0, 50, 0, 0, 'PreD'],[0, 10, 8, 0, 'Tone'],[0, 100, 52, 0, 'Mix'],[0, 0, 0, 0, '-'],[0, 0, 0, 0, '-'],[0, 0, 0, 0, '-'],[0, 0, 0, 0, '-']]],
['PitchSHFT',100663472,6,'PITCHSHF.ZD2.BMP',1,4,[[0, 25, 19, 0, 'Shift'],[0, 50, 25, 0, 'Fine'],[0, 10, 7, 0, 'Tone'],[0, 100, 40, 0, 'BAL'],[0, 0, 0, 0, '-'],[0, 0, 0, 0, '-'],[0, 0, 0, 0, '-'],[0, 0, 0, 0, '-']]],
['MonoPitch',100663488,6,'MONOPITC.ZD2.BMP',1,4,[[0, 25, 0, 0, 'Shift'],[0, 50, 25, 0, 'Fine'],[0, 10, 6, 0, 'Tone'],[0, 100, 50, 0, 'BAL'],[0, 0, 0, 0, '-'],[0, 0, 0, 0, '-'],[0, 0, 0, 0, '-'],[0, 0, 0, 0, '-']]],
['HPS',100663504,6,'HPS.ZD2.BMP',1,4,[[0, 9, 6, 0, 'Scale'],[0, 11, 0, 0, 'Key'],[0, 10, 6, 0, 'Tone'],[0, 100, 70, 0, 'Mix'],[0, 0, 0, 0, '-'],[0, 0, 0, 0, '-'],[0, 0, 0, 0, '-'],[0, 0, 0, 0, '-']]],
['Slicer',100663536,6,'SLICER.ZD2.BMP',1,4,[[0, 19, 0, 0, 'PTTRN'],[0, 77, 24, 0, 'Speed'],[0, 50, 20, 0, 'THRSH'],[0, 100, 87, 0, 'VOL'],[0, 0, 0, 0, '-'],[0, 0, 0, 0, '-'],[0, 0, 0, 0, '-'],[0, 0, 0, 0, '-']]],
['CloneCho',100663552,6,'CLONECHO.ZD2.BMP',1,4,[[0, 1, 1, 0, 'Depth'],[0, 100, 23, 0, 'Rate'],[0, 100, 100, 0, 'Tone'],[0, 100, 100, 0, 'Mix'],[0, 0, 0, 0, '-'],[0, 0, 0, 0, '-'],[0, 0, 0, 0, '-'],[0, 0, 0, 0, '-']]],
['SuperCho',100663568,6,'SUPERCHO.ZD2.BMP',1,4,[[0, 100, 50, 0, 'Depth'],[0, 100, 50, 0, 'Rate'],[0, 100, 50, 0, 'Tone'],[0, 100, 42, 0, 'Mix'],[0, 0, 0, 0, '-'],[0, 0, 0, 0, '-'],[0, 0, 0, 0, '-'],[0, 0, 0, 0, '-']]],
['StonePha',100663584,6,'STONEPHA.ZD2.BMP',1,4,[[0, 1, 0, 0, 'Color'],[0, 100, 100, 0, 'Depth'],[0, 100, 50, 0, 'Rate'],[0, 100, 40, 0, 'RESO'],[0, 0, 0, 0, '-'],[0, 0, 0, 0, '-'],[0, 0, 0, 0, '-'],[0, 0, 0, 0, '-']]],
['CoronaTri',100663601,6,'CRNTRI3S.ZD2.BMP',1,4,[[0, 100, 100, 0, 'Depth'],[0, 100, 25, 0, 'Speed'],[0, 100, 100, 0, 'Tone'],[0, 100, 100, 0, 'Mix'],[0, 0, 0, 0, '-'],[0, 0, 0, 0, '-'],[0, 0, 0, 0, '-'],[0, 0, 0, 0, '-']]],
['BendCho',100663616,6,'BENDCHO.ZD2.BMP',1,4,[[0, 1, 0, 0, 'Mode'],[0, 100, 40, 0, 'Depth'],[0, 50, 50, 0, 'Time'],[0, 100, 100, 0, 'BAL'],[0, 0, 0, 0, '-'],[0, 0, 0, 0, '-'],[0, 0, 0, 0, '-'],[0, 0, 0, 0, '-']]],
['AnalogCho',100663632,6,'ANA234CH.ZD2.BMP',1,4,[[0, 100, 52, 0, 'Depth'],[0, 100, 54, 0, 'Rate'],[0, 100, 49, 0, 'Tone'],[0, 100, 82, 0, 'Mix'],[0, 0, 0, 0, '-'],[0, 0, 0, 0, '-'],[0, 0, 0, 0, '-'],[0, 0, 0, 0, '-']]],
['WarpPhase',100663648,6,'WRPPHASE.ZD2.BMP',1,4,[[0, 1, 0, 0, 'Mode'],[0, 77, 24, 0, 'Speed'],[0, 10, 7, 0, 'RESO'],[0, 100, 80, 0, 'VOL'],[0, 0, 0, 0, '-'],[0, 0, 0, 0, '-'],[0, 0, 0, 0, '-'],[0, 0, 0, 0, '-']]],
['Duo Phase',100663665,6,'DUOPHA1U.ZD2.BMP',2,8,[[0, 99, 62, 0, 'DPT A'],[0, 77, 5, 0, 'RateA'],[0, 10, 6, 0, 'ResoA'],[0, 2, 0, 0, 'Link'],[0, 99, 36, 0, 'DPT B'],[0, 51, 46, 0, 'RateB'],[0, 10, 0, 0, 'ResoB'],[0, 100, 80, 0, 'VOL']]],
['Bomber',117440528,7,'BOMBER.ZD2.BMP',1,4,[[0, 99, 49, 0, 'Decay'],[0, 10, 4, 0, 'Tone'],[0, 100, 30, 0, 'Mix'],[0, 1, 1, 0, 'ON/OFF'],[0, 0, 0, 0, '-'],[0, 0, 0, 0, '-'],[0, 0, 0, 0, '-'],[0, 0, 0, 0, '-']]],
['AutoPan',117440544,7,'AUTOPAN.ZD2.BMP',1,4,[[0, 78, 5, 0, 'Rate'],[0, 50, 50, 0, 'Width'],[0, 10, 0, 0, 'Clip'],[0, 100, 80, 0, 'VOL'],[0, 0, 0, 0, '-'],[0, 0, 0, 0, '-'],[0, 0, 0, 0, '-'],[0, 0, 0, 0, '-']]],
['LoopRoll',117440577,7,'LPROLL3S.ZD2.BMP',1,4,[[0, 3006, 2992, 0, 'Time'],[0, 75, 75, 0, 'Duty'],[0, 100, 100, 0, 'BAL'],[0, 1, 1, 0, 'ON/OFF'],[0, 0, 0, 0, '-'],[0, 0, 0, 0, '-'],[0, 0, 0, 0, '-'],[0, 0, 0, 0, '-']]],
['HotSpice',117440592,7,'HOTSPICE.ZD2.BMP',1,4,[[0, 100, 11, 0, 'Bend'],[0, 100, 57, 0, 'Buzz'],[0, 100, 36, 0, '+1oct'],[0, 100, 80, 0, 'VOL'],[0, 0, 0, 0, '-'],[0, 0, 0, 0, '-'],[0, 0, 0, 0, '-'],[0, 0, 0, 0, '-']]],
['Delay',134217745,8,'DELAY_3S.ZD2.BMP',1,4,[[0, 3018, 559, 0, 'Time'],[0, 100, 30, 0, 'F.B'],[0, 100, 70, 0, 'Mix'],[0, 1, 0, 0, 'Tail'],[0, 0, 0, 0, '-'],[0, 0, 0, 0, '-'],[0, 0, 0, 0, '-'],[0, 0, 0, 0, '-']]],
['AnalogDly',134217761,8,'ANDLY_3S.ZD2.BMP',1,4,[[0, 3018, 359, 0, 'Time'],[0, 100, 28, 0, 'F.B'],[0, 100, 40, 0, 'Mix'],[0, 1, 0, 0, 'Tail'],[0, 0, 0, 0, '-'],[0, 0, 0, 0, '-'],[0, 0, 0, 0, '-'],[0, 0, 0, 0, '-']]],
['TapeEcho',134217776,8,'TAPEECHO.ZD2.BMP',1,4,[[0, 2014, 559, 0, 'Time'],[0, 100, 64, 0, 'F.B'],[0, 100, 56, 0, 'Mix'],[0, 1, 0, 0, 'Tail'],[0, 0, 0, 0, '-'],[0, 0, 0, 0, '-'],[0, 0, 0, 0, '-'],[0, 0, 0, 0, '-']]],
['ReverseDL',134217793,8,'RVRSDL3S.ZD2.BMP',1,4,[[0, 1503, 990, 0, 'Time'],[0, 100, 20, 0, 'F.B'],[0, 100, 50, 0, 'BAL'],[0, 1, 0, 0, 'Tail'],[0, 0, 0, 0, '-'],[0, 0, 0, 0, '-'],[0, 0, 0, 0, '-'],[0, 0, 0, 0, '-']]],
['ModDelay',134217808,8,'MODDELAY.ZD2.BMP',1,4,[[0, 2014, 499, 0, 'Time'],[0, 100, 50, 0, 'F.B'],[0, 100, 62, 0, 'Mix'],[0, 1, 0, 0, 'Tail'],[0, 0, 0, 0, '-'],[0, 0, 0, 0, '-'],[0, 0, 0, 0, '-'],[0, 0, 0, 0, '-']]],
['P-P Delay',134217857,8,'PPDLY_3S.ZD2.BMP',1,4,[[0, 3018, 559, 0, 'Time'],[0, 100, 30, 0, 'F.B'],[0, 100, 70, 0, 'Mix'],[0, 1, 0, 0, 'Tail'],[0, 0, 0, 0, '-'],[0, 0, 0, 0, '-'],[0, 0, 0, 0, '-'],[0, 0, 0, 0, '-']]],
['FilterDly',134217872,8,'FLTRDLY.ZD2.BMP',1,4,[[0, 2014, 499, 0, 'Time'],[0, 100, 50, 0, 'F.B'],[0, 100, 90, 0, 'Mix'],[0, 1, 0, 0, 'Tail'],[0, 0, 0, 0, '-'],[0, 0, 0, 0, '-'],[0, 0, 0, 0, '-'],[0, 0, 0, 0, '-']]],
['Dual DLY',134217889,8,'DUALDL3S.ZD2.BMP',2,8,[[0, 1503, 500, 0, 'TimeA'],[0, 110, 50, 0, 'F.B A'],[0, 1503, 375, 0, 'TimeB'],[0, 110, 50, 0, 'F.B B'],[0, 100, 25, 0, 'DlyMx'],[0, 100, 50, 0, 'BAL'],[0, 101, 0, 0, 'Depth'],[0, 50, 25, 0, 'Speed']]],
['Pitch DLY',134217905,8,'PTCHDL3S.ZD2.BMP',1,4,[[0, 30, 21, 0, 'Pitch'],[0, 1999, 89, 0, 'Time'],[0, 100, 80, 0, 'F.B'],[0, 100, 80, 0, 'Mix'],[0, 0, 0, 0, '-'],[0, 0, 0, 0, '-'],[0, 0, 0, 0, '-'],[0, 0, 0, 0, '-']]],
['SlapBackD',134217921,8,'SLPBKD3S.ZD2.BMP',1,4,[[0, 300, 98, 0, 'Time'],[0, 100, 29, 0, 'F.B'],[0, 100, 40, 0, 'Mix'],[0, 2, 0, 0, 'SubDv'],[0, 0, 0, 0, '-'],[0, 0, 0, 0, '-'],[0, 0, 0, 0, '-'],[0, 0, 0, 0, '-']]],
['A-Pan DLY',134217937,8,'APANDL3S.ZD2.BMP',2,7,[[0, 1512, 222, 0, 'Time'],[0, 100, 87, 0, 'F.B'],[0, 100, 53, 0, 'Mix'],[0, 1, 1, 0, 'Link'],[0, 52, 26, 0, 'Cycle'],[0, 50, 50, 0, 'Width'],[0, 10, 0, 0, 'Clip'],[0, 0, 0, 0, '-']]],
['PhaseDly',134217953,8,'PHASDL1U.ZD2.BMP',2,8,[[0, 2014, 2006, 0, 'Time'],[0, 100, 24, 0, 'F.B'],[0, 100, 56, 0, 'Mix'],[0, 1, 1, 0, 'Tail'],[0, 3, 2, 0, 'Color'],[0, 100, 100, 0, 'Depth'],[0, 77, 59, 0, 'Rate'],[0, 100, 48, 0, 'Reso']]],
['TapeEcho3',134217969,8,'TPEC3_3S.ZD2.BMP',2,8,[[0, 100, 50, 0, 'Gain'],[0, 100, 62, 0, 'Hi'],[0, 100, 47, 0, 'Lo'],[0, 100, 80, 0, 'VOL'],[0, 1005, 350, 0, 'Time'],[0, 100, 20, 0, 'F.B'],[0, 100, 50, 0, 'Mix'],[0, 100, 50, 0, 'RecLv']]],
['ICE Delay',134217985,8,'ICEDLY3S.ZD2.BMP',1,4,[[0, 30, 28, 0, 'INTVL'],[0, 931, 928, 0, 'Time'],[0, 100, 46, 0, 'F.B'],[0, 100, 36, 0, 'Mix'],[0, 0, 0, 0, '-'],[0, 0, 0, 0, '-'],[0, 0, 0, 0, '-'],[0, 0, 0, 0, '-']]],
['SlwAtkDly',134218001,8,'SLATDL3S.ZD2.BMP',1,4,[[0, 49, 24, 0, 'Swell'],[0, 1411, 489, 0, 'Time'],[0, 100, 71, 0, 'F.B'],[0, 100, 64, 0, 'Mix'],[0, 0, 0, 0, '-'],[0, 0, 0, 0, '-'],[0, 0, 0, 0, '-'],[0, 0, 0, 0, '-']]],
['SoftEcho',134218017,8,'SOFTEC3S.ZD2.BMP',1,4,[[0, 1, 1, 0, 'MOD'],[0, 562, 387, 0, 'Time'],[0, 100, 47, 0, 'F.B'],[0, 100, 69, 0, 'Mix'],[0, 0, 0, 0, '-'],[0, 0, 0, 0, '-'],[0, 0, 0, 0, '-'],[0, 0, 0, 0, '-']]],
['Air',150994960,9,'AIR.ZD2.BMP',1,4,[[0, 99, 19, 0, 'Size'],[0, 10, 5, 0, 'REF'],[0, 100, 60, 0, 'Mix'],[0, 1, 0, 0, 'Tail'],[0, 0, 0, 0, '-'],[0, 0, 0, 0, '-'],[0, 0, 0, 0, '-'],[0, 0, 0, 0, '-']]],
['Room',150994976,9,'ROOM.ZD2.BMP',1,4,[[0, 99, 4, 0, 'PreD'],[0, 29, 9, 0, 'Decay'],[0, 100, 60, 0, 'Mix'],[0, 1, 0, 0, 'Tail'],[0, 0, 0, 0, '-'],[0, 0, 0, 0, '-'],[0, 0, 0, 0, '-'],[0, 0, 0, 0, '-']]],
['Hall',150994992,9,'HALL.ZD2.BMP',1,4,[[0, 99, 48, 0, 'PreD'],[0, 29, 9, 0, 'Decay'],[0, 100, 46, 0, 'Mix'],[0, 1, 0, 0, 'Tail'],[0, 0, 0, 0, '-'],[0, 0, 0, 0, '-'],[0, 0, 0, 0, '-'],[0, 0, 0, 0, '-']]],
['HD Hall',150995008,9,'HD_HALL.ZD2.BMP',1,4,[[0, 199, 80, 0, 'PreD'],[0, 100, 45, 0, 'Decay'],[0, 100, 62, 0, 'Mix'],[0, 1, 0, 0, 'Tail'],[0, 0, 0, 0, '-'],[0, 0, 0, 0, '-'],[0, 0, 0, 0, '-'],[0, 0, 0, 0, '-']]],
['Spring',150995024,9,'SPRING.ZD2.BMP',1,4,[[0, 99, 0, 0, 'PreD'],[0, 29, 19, 0, 'Decay'],[0, 100, 50, 0, 'Mix'],[0, 1, 0, 0, 'Tail'],[0, 0, 0, 0, '-'],[0, 0, 0, 0, '-'],[0, 0, 0, 0, '-'],[0, 0, 0, 0, '-']]],
['FD Spring',150995040,9,'FDSPRING.ZD2.BMP',1,4,[[0, 1, 0, 0, 'Color'],[0, 100, 100, 0, 'Lo'],[0, 100, 100, 0, 'Hi'],[0, 100, 50, 0, 'Mix'],[0, 0, 0, 0, '-'],[0, 0, 0, 0, '-'],[0, 0, 0, 0, '-'],[0, 0, 0, 0, '-']]],
['Plate',150995056,9,'PLATEREV.ZD2.BMP',1,4,[[0, 199, 8, 0, 'PreD'],[0, 100, 52, 0, 'Decay'],[0, 100, 44, 0, 'Mix'],[0, 1, 0, 0, 'Tail'],[0, 0, 0, 0, '-'],[0, 0, 0, 0, '-'],[0, 0, 0, 0, '-'],[0, 0, 0, 0, '-']]],
['EarlyRef',150995072,9,'EARLYREF.ZD2.BMP',1,4,[[0, 29, 14, 0, 'Decay'],[0, 20, 20, 0, 'Shape'],[0, 10, 6, 0, 'Tone'],[0, 100, 50, 0, 'Mix'],[0, 0, 0, 0, '-'],[0, 0, 0, 0, '-'],[0, 0, 0, 0, '-'],[0, 0, 0, 0, '-']]],
['Church',150995104,9,'CHURCH.ZD2.BMP',1,4,[[0, 200, 96, 0, 'PreD'],[0, 100, 49, 0, 'Decay'],[0, 100, 46, 0, 'Mix'],[0, 1, 0, 0, 'Tail'],[0, 0, 0, 0, '-'],[0, 0, 0, 0, '-'],[0, 0, 0, 0, '-'],[0, 0, 0, 0, '-']]],
['Chamber',150995152,9,'CHAMBER.ZD2.BMP',1,4,[[0, 200, 24, 0, 'PreD'],[0, 100, 50, 0, 'Decay'],[0, 100, 48, 0, 'Mix'],[0, 1, 1, 0, 'Tail'],[0, 0, 0, 0, '-'],[0, 0, 0, 0, '-'],[0, 0, 0, 0, '-'],[0, 0, 0, 0, '-']]],
['GateRev',150995168,9,'GATE_REV.ZD2.BMP',1,4,[[0, 4, 0, 0, 'Color'],[0, 100, 55, 0, 'Decay'],[0, 100, 50, 0, 'Tone'],[0, 100, 60, 0, 'BAL'],[0, 0, 0, 0, '-'],[0, 0, 0, 0, '-'],[0, 0, 0, 0, '-'],[0, 0, 0, 0, '-']]],
['PDL Vol',184549392,11,'PDL_VOL.ZD2.BMP',1,4,[[1, 100, 100, 0, 'VOL'],[0, 100, 0, 0, 'Min'],[0, 100, 100, 0, 'Max'],[0, 1, 0, 0, 'Curve'],[0, 0, 0, 0, '-'],[0, 0, 0, 0, '-'],[0, 0, 0, 0, '-'],[0, 0, 0, 0, '-']]],
['BlackWah',184549408,11,'BLCK_WAH.ZD2.BMP',1,4,[[1, 100, 50, 0, 'FREQ'],[0, 100, 50, 0, 'Range'],[0, 100, 0, 0, 'Dry'],[0, 100, 80, 0, 'VOL'],[0, 0, 0, 0, '-'],[0, 0, 0, 0, '-'],[0, 0, 0, 0, '-'],[0, 0, 0, 0, '-']]],
['ChromeWah',184549424,11,'CHRM_WAH.ZD2.BMP',1,4,[[1, 100, 50, 0, 'FREQ'],[0, 100, 50, 0, 'Range'],[0, 100, 0, 0, 'Dry'],[0, 100, 80, 0, 'VOL'],[0, 0, 0, 0, '-'],[0, 0, 0, 0, '-'],[0, 0, 0, 0, '-'],[0, 0, 0, 0, '-']]],
['WAH100',184549440,11,'WH100.ZD2.BMP',1,4,[[1, 50, 25, 0, 'FREQ'],[0, 100, 40, 0, 'Depth'],[0, 100, 0, 0, 'Dry'],[0, 100, 80, 0, 'VOL'],[0, 0, 0, 0, '-'],[0, 0, 0, 0, '-'],[0, 0, 0, 0, '-'],[0, 0, 0, 0, '-']]],
['PDL Pitch',184549456,11,'PDL_PIT.ZD2.BMP',1,4,[[1, 100, 0, 0, 'Bend'],[0, 8, 0, 0, 'Color'],[0, 10, 10, 0, 'Tone'],[0, 1, 0, 0, 'Mode'],[0, 0, 0, 0, '-'],[0, 0, 0, 0, '-'],[0, 0, 0, 0, '-'],[0, 0, 0, 0, '-']]],
['PDL MnPit',184549472,11,'PDL_MNPT.ZD2.BMP',1,4,[[1, 100, 0, 0, 'Bend'],[0, 8, 0, 0, 'Color'],[0, 10, 10, 0, 'Tone'],[0, 1, 0, 0, 'Mode'],[0, 0, 0, 0, '-'],[0, 0, 0, 0, '-'],[0, 0, 0, 0, '-'],[0, 0, 0, 0, '-']]],
['PDL Vibe',184549488,11,'PDL_VIBE.ZD2.BMP',1,4,[[1, 50, 25, 0, 'Speed'],[0, 100, 60, 0, 'Depth'],[0, 1, 1, 0, 'Mode'],[0, 100, 80, 0, 'VOL'],[0, 0, 0, 0, '-'],[0, 0, 0, 0, '-'],[0, 0, 0, 0, '-'],[0, 0, 0, 0, '-']]],
['PDL Drive',184549504,11,'PDL_DRV.ZD2.BMP',1,4,[[1, 100, 50, 0, 'Gain'],[0, 100, 74, 0, 'Tone'],[0, 100, 48, 0, 'PRSNC'],[0, 100, 61, 0, 'VOL'],[0, 0, 0, 0, '-'],[0, 0, 0, 0, '-'],[0, 0, 0, 0, '-'],[0, 0, 0, 0, '-']]],
['PDL PHSR',184549520,11,'PDL_PHA.ZD2.BMP',1,4,[[1, 49, 11, 0, 'Rate'],[0, 100, 100, 0, 'Depth'],[0, 100, 50, 0, 'RESO'],[0, 3, 3, 0, 'Color'],[0, 0, 0, 0, '-'],[0, 0, 0, 0, '-'],[0, 0, 0, 0, '-'],[0, 0, 0, 0, '-']]],
['PDL Delay',184549537,11,'PDLDLY3S.ZD2.BMP',1,4,[[1, 100, 100, 0, 'InLvl'],[0, 3018, 359, 0, 'Time'],[0, 100, 40, 0, 'F.B'],[0, 100, 100, 0, 'Mix'],[0, 0, 0, 0, '-'],[0, 0, 0, 0, '-'],[0, 0, 0, 0, '-'],[0, 0, 0, 0, '-']]],
['PDL Rev',184549552,11,'PDL_REV.ZD2.BMP',1,4,[[1, 100, 100, 0, 'InLvl'],[0, 99, 48, 0, 'PreD'],[0, 29, 14, 0, 'Decay'],[0, 100, 80, 0, 'Mix'],[0, 0, 0, 0, '-'],[0, 0, 0, 0, '-'],[0, 0, 0, 0, '-'],[0, 0, 0, 0, '-']]],
['OSC Echo',184549569,11,'OSCECH3S.ZD2.BMP',1,4,[[1, 100, 0, 0, 'OSC'],[0, 481, 311, 0, 'T-Min'],[0, 481, 81, 0, 'T-Max'],[0, 100, 80, 0, 'Mix'],[0, 0, 0, 0, '-'],[0, 0, 0, 0, '-'],[0, 0, 0, 0, '-'],[0, 0, 0, 0, '-']]],
['VoiceWah',184549584,11,'VOICE_WH.ZD2.BMP',1,4,[[1, 100, 0, 0, 'Vowel'],[0, 2, 1, 0, 'PTTRN'],[0, 100, 50, 0, 'Voice'],[0, 1, 0, 0, 'Mode'],[0, 0, 0, 0, '-'],[0, 0, 0, 0, '-'],[0, 0, 0, 0, '-'],[0, 0, 0, 0, '-']]],
['PDL Roto',184549601,11,'PDLROT3S.ZD2.BMP',1,4,[[1, 1, 0, 0, 'Mode'],[0, 100, 20, 0, 'Drive'],[0, 100, 50, 0, 'BAL'],[0, 100, 80, 0, 'VOL'],[0, 0, 0, 0, '-'],[0, 0, 0, 0, '-'],[0, 0, 0, 0, '-'],[0, 0, 0, 0, '-']]],
['P-BitCRSH',184549616,11,'PDL_BITC.ZD2.BMP',1,4,[[1, 50, 2, 0, 'SMPL'],[0, 13, 5, 0, 'Bit'],[0, 10, 8, 0, 'Tone'],[0, 100, 90, 0, 'BAL'],[0, 0, 0, 0, '-'],[0, 0, 0, 0, '-'],[0, 0, 0, 0, '-'],[0, 0, 0, 0, '-']]],
['PDL FLNGR',184549632,11,'PDL_FLNG.ZD2.BMP',1,4,[[1, 100, 50, 0, 'FREQ'],[0, 20, 18, 0, 'RESO'],[0, 10, 8, 0, 'HiDMP'],[0, 100, 65, 0, 'Mix'],[0, 0, 0, 0, '-'],[0, 0, 0, 0, '-'],[0, 0, 0, 0, '-'],[0, 0, 0, 0, '-']]],
['PDL Reso',192938016,11,'PDL_RESO.ZD2.BMP',1,4,[[1, 49, 11, 0, 'FREQ'],[0, 10, 7, 0, 'RESO'],[0, 100, 50, 0, 'Dry'],[0, 100, 92, 0, 'VOL'],[0, 0, 0, 0, '-'],[0, 0, 0, 0, '-'],[0, 0, 0, 0, '-'],[0, 0, 0, 0, '-']]],
['Output VP',199294960,11,'OUT_VP.ZD2.BMP',1,1,[[0, 5075, 4947, 0, '-'],[0, 0, 0, 0, '-'],[0, 0, 0, 0, '-'],[0, 0, 0, 0, '-'],[0, 0, 0, 0, '-'],[0, 0, 0, 0, '-'],[0, 0, 0, 0, '-'],[0, 0, 0, 0, '-']]]
]
